bebenlebricolo/LabBenchPowerSupply/Simulations/MosfetDriverAntiLatchup.asc

C1: cap; 10µ
Q1: npn; 2N2222
Q2: pnp; 2N2907
Q3: npn; 2N2222
Q4: pnp; 2N2907
R1: res; 1k
R2: res; 56k
R3: res; 1k
R4: res; 56k
R5: res; 56k
R6: res; 1k
R7: res; 56k
R8: res; 1k
R9: res; 200
V1: voltage; 5
V2: voltage; 10
V3: signal; PULSE(0 5 0 1n 1n 10m 20m 250)
Named nets: 0, 5V, 10V
.tran 0 100m 1m 100u
