bebenlebricolo/LabBenchPowerSupply/Simulations/MosfetDriverAntiLatchup_P.asc

C1: cap; 470µ
D1: schottky; MBR745
L1: ind; 110µ
M1: pmos; FDC5614P
Q1: npn; 2N2222
Q2: pnp; 2N2907
Q3: npn; 2N2222
Q4: npn; 2N2222
R1: res; 1k
R2: res; 56k
R3: res; 1k
R4: res; 56k
R5: res; 56k
R6: res; 1k
R7: res; 10
R8: res; 1k
R9: res; 56k
V1: voltage; 5
V2: voltage; 30
V3: signal; PULSE(0 5 0 1n 1n 10m 20m 250)
V4: signal; PULSE(0 5 11m 1n 1n 8m 20m 250)
Named nets: 0, 5V, DriverSupply, high_side, low_side, MosfetGate
.tran 0 100m 1m 100u
