bebenlebricolo/LabBenchPowerSupply/Simulations/BuckConverter.asc

C1: cap; 470µ
C2: cap; 1µ
D1: schottky; MBR0530L
L1: ind; 110µ; Ipk=7
M1: nmos; AP9465GEM
R1: res; 1
R2: res; 0.1
U2: AD8032
V1: voltage; 12
V2: signal; PULSE(0 12 0 1n 1n 30u 50u 5K)
Named nets: 0, Mosfet_control, Out, Vshunt, Vcc, FilteredVshunt
.tran 0 20m 1n 1m startup
