bebenlebricolo/LabBenchPowerSupply/Firmware/Drivers/Adc/inc/adc.h

/*

------------------
@<FreeMyCode>
FreeMyCode version : 1.0 RC alpha
    Author : bebenlebricolo
    License : 
        name : GPLv3
        url : https://www.gnu.org/licenses/quick-guide-gplv3.html
    Date : 12/02/2021
    Project : LabBenchPowerSupply
    Description : The Lab Bench Power Supply provides a simple design based around an Arduino Nano board to convert AC main voltage into
 smaller ones, ranging from 0V to 16V, with voltage and current regulations
<FreeMyCode>@
------------------

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
You should have received a copy of the GNU General Public License
along with this program.  If not, see <https://www.gnu.org/licenses/>.
*/

/**
 * @brief ADC custom driver
*/
#ifndef ADC_HEADER
#define ADC_HEADER

/* Expose this API to C++ code without name mangling */
#ifdef __cplusplus
extern "C"
{
#endif /* __cplusplus */

/* Generic includes */
#include <stdint.h>
#include <stddef.h>
#include <stdbool.h>

/* Application drivers */
#include "adc_reg.h"

/* ############################################################################################
   ################################## Data types declaration ##################################
   ############################################################################################ */

typedef uint16_t adc_result_t;
typedef uint16_t adc_millivolts_t;


/**
 * @brief generic structure which holds timer error types
*/
typedef enum
{
    ADC_ERROR_OK,               /**< Everything went well so far                                  */
    ADC_ERROR_CONFIG,           /**< Given configuration is not well-formed                       */
    ADC_ERROR_CHANNEL_NOT_FOUND,/**< Given configuration is not well-formed                       */
    ADC_ERROR_NULL_POINTER,     /**< One or more parameters were set to NULL                      */
    ADC_ERROR_NULL_HANDLE,      /**< Timer handle still points to NULL                            */
    ADC_ERROR_UNKNOWN_TIMER,    /**< Given timer id exceeds the range of registered timers        */
    ADC_ERROR_NOT_INITIALISED,  /**< Given configuration is not well-formed                       */
} adc_error_t;

/**
 * @brief basic adc peripheral state
*/
typedef enum
{
    ADC_STATE_READY,              /**< Adc is initialised and is ready                */
    ADC_STATE_BUSY,               /**< A conversion is ongoing, peripheral is busy    */
    ADC_STATE_NOT_INITIALISED,    /**< Driver is not initialised                      */
} adc_state_t;

/**
 * @brief gives running modes of ADC driver
*/
typedef enum
{
    ADC_RUNNING_MODE_SINGLE_SHOT,   /**< If set, adc will require start() to be called repeateadly between each calls       */
    ADC_RUNNING_MODE_AUTOTRIGGERED  /**< ADC is controlled by a trigger event, which my be set to free-running (software)
                                         in this particular case, ADC will be continuously triggered when a conversion ends  */
}adc_running_mode_t;

/**
 * @brief this structure mimics ADC peripheral registers. It is passed when configuring ADC peripheral.
 */
typedef struct {
    volatile uint8_t  *  mux_reg;    /**< Refers to adc multiplexing register (ADCMUX)   */
    volatile uint8_t  *  adcsra_reg; /**< Refers to ADC Control and Status Register A    */
    volatile uint8_t  *  adcsrb_reg; /**< Refers to ADC Control and Status Register B    */

    /* Packs result registers in one */
    struct {
        volatile uint8_t *  adclow_reg;  /**< Refers to the low value register of ADC peripheral  (first 8 bits)*/
        volatile uint8_t *  adchigh_reg; /**< Refers to the high value register of ADC peripheral (last 2 bits) */
    } readings;
} adc_handle_t;

/* Configuration structure of ADC module */
typedef struct {
    uint16_t                    supply_voltage_mv;  /**< MCU supply voltage in millivolts                       */
    adc_prescaler_t             prescaler;          /**< ADC internal prescaler                                 */
    adc_voltage_ref_t           ref;                /**< ADC reference voltage                                  */
    adc_result_align_t          alignment;          /**< ADC data alignment                                     */
    adc_running_mode_t          running_mode;       /**< Select the mode between continous or single shot       */
    adc_autotrigger_sources_t   trigger_sources;    /**< ADC trigger mode                                       */
    adc_handle_t                handle;             /**< Packs pointers to base ADC registers. Particularly
                                                         useful when performing Dependency Injection & testing  */
    bool using_interrupt;                           /**< uses interrupts for data fetch process or not          */
} adc_config_hal_t;


/* ############################################################################################
   #################################### Types manipulators ####################################
   ############################################################################################ */

/**
 * @brief copies a configuration from a source pointer to a destination pointer
 * @param[in]   src     : pointer to source object
 * @param[out]  dest    : pointer to destination object
 * @return
 *      PERIPHERAL_ERROR_OK             : operation succeeded
 *      PERIPHERAL_ERROR_NULL_POINTER   : null pointer guarded
*/
adc_error_t adc_config_hal_copy(adc_config_hal_t * dest, adc_config_hal_t * const src);

/**
 * @brief resets config to default
 * @param[in]   config : pointer to configuration object
 * @return
 *      PERIPHERAL_ERROR_OK             : operation succeeded
 *      PERIPHERAL_ERROR_NULL_POINTER   : null pointer guarded
*/
adc_error_t adc_config_hal_reset(adc_config_hal_t * config);

/**
 * @brief returns a default configuration for the ADC driver
 * @param[out]  config : pointer to configuration object
 * @return
 *      PERIPHERAL_ERROR_OK             : operation succeeded
 *      PERIPHERAL_ERROR_NULL_POINTER   : null pointer guarded
*/
adc_error_t adc_config_hal_get_default(adc_config_hal_t * config);

/**
 * @brief copies handle data from a source object to destination object
 * @param[in]   src     : pointer to source object
 * @param[out]  dest    : pointer to destination object
 * @return
 *      PERIPHERAL_ERROR_OK             : operation succeeded
 *      PERIPHERAL_ERROR_NULL_POINTER   : null pointer guarded
*/
adc_error_t adc_handle_copy(adc_handle_t * const dest, const adc_handle_t * const src);

/**
 * @brief resets handle to default
 * @param[in]   handle : pointer to handle object
 * @return
 *      PERIPHERAL_ERROR_OK             : operation succeeded
 *      PERIPHERAL_ERROR_NULL_POINTER   : null pointer guarded
*/
adc_error_t adc_handle_reset(adc_handle_t * const handle);

/* ############################################################################################
   ################################## Function declarations ###################################
   ############################################################################################ */

/**
 * @brief adc module initialisation function
*/
adc_error_t adc_base_init(adc_config_hal_t * const config);

/**
 * @brief module deinitialisation
*/
void adc_base_deinit(void);

/**
 * @brief starts the adc in normal mode, no interrupt set
 * @see adc_state_t adc_process() to be able to fetch results from adc registers and post result to internal buffer
 * Note: one must use functions in this order :
 *    - adc_base_init() // done once
 *    - adc_start()     // starts peripheral
 *    - repeat :
 *       - if interrupt mode is not set : adc_process()   // fetches result from adc peripheral
 *       - adc_read_raw()       // return results to application
 *    OR - adc_read_millivolt() // instead to retrieve actual voltage instead of raw value
 *    - adc_stop()      // stops the adc
 * @return
 *      PERIPHERAL_ERROR_OK      : operation was successful
 *      ADC_ERROR_CONFIG  : adc peripheral is not enabled (not initialised ?)
*/
adc_state_t adc_start(void);

/**
 * @brief stops the adc in normal mode, no interrupt
 * @return
 *      PERIPHERAL_ERROR_OK      : operation was successful
 *      ADC_ERROR_CONFIG  : adc peripheral is not enabled (not initialised ?)
*/
adc_state_t adc_stop(void);

/**
 * @brief starts conversions and retrieves results (using asynchronous, non interrupting mode)
 * @return
 *      PERIPHERAL_ERROR_OK      : operation was successful
 *      ADC_ERROR_CONFIG  : adc peripheral is not enabled (not initialised ?)
*/
adc_state_t adc_process(void);

/**
 * @brief isr handler that might be called from within an ISR function
*/
void adc_isr_handler(void);

/**
 * @brief explicitely adds a channel to scanned channels configuration
 * @param[in]   channel : channel to be configured and scanned */
adc_error_t adc_register_channel(const adc_mux_t channel);

/**
 * @brief explicitely removes channel from scanned channels configuration
 * @param[in]   channel : channel to be removed */
adc_error_t adc_unregister_channel(const adc_mux_t channel);

/**
 * @brief adc result getter function
 * @param[in]   channel  : targeted device index
 * @param[out]  result   : last fetched result from this device
 * @return
 *      PERIPHERAL_ERROR_OK             : everything's fine
 *      PERIPHERAL_ERROR_NULL_POINTER   : wrong pointer or out of bounds index
*/
adc_error_t adc_read_raw(const adc_mux_t channel, adc_result_t * const result);

/**
 * @brief adc raw reading getter
 * @param[in]   channel   : targeted device index
 * @param[out]  reading : last fetched result from this device
 * @return
 *      PERIPHERAL_ERROR_OK      : everything's fine
 *      PERIPHERAL_ERROR_NULL_POINTER  : wrong pointer or out of bounds index
*/
adc_error_t adc_read_millivolt(const adc_mux_t channel, adc_millivolts_t * const reading);


#ifdef __cplusplus
}
#endif

#endif /* ADC_HEADER */
