bebenlebricolo/LabBenchPowerSupply/Firmware/Sensors/Thermistor/Tests/thermistor_driver_tests.cpp

/*

------------------
@<FreeMyCode>
FreeMyCode version : 1.0 RC alpha
    Author : bebenlebricolo
    License :
        name : GPLv3
        url : https://www.gnu.org/licenses/quick-guide-gplv3.html
    Date : 12/02/2021
    Project : LabBenchPowerSupply
    Description : The Lab Bench Power Supply provides a simple design based around an Arduino Nano board to convert AC main voltage into
 smaller ones, ranging from 0V to 16V, with voltage and current regulations
<FreeMyCode>@
------------------

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
You should have received a copy of the GNU General Public License
along with this program.  If not, see <https://www.gnu.org/licenses/>.
*/

#include "gtest/gtest.h"

#include "config.h"
#include "adc_stub.h"
#include "thermistor.h"
#include "thermistor_private.h"

TEST(thermistor_tests, test_find_segment)
{
    uint8_t target_ratio = 11;
    thermistor_curve_discrete_pair_t const * lower_bound = NULL;
    thermistor_curve_discrete_pair_t const * upper_bound = NULL;
    bool ret = find_segment(thermistor_driver_config[0].model.curve.data.discrete.cold_side, target_ratio, RATIO_COEF_1, &lower_bound, &upper_bound );
    ASSERT_TRUE(ret);
    ASSERT_EQ(lower_bound->ratio, 12U);
    ASSERT_EQ(upper_bound->ratio, 8U);

    // Using the x10 representation, actual ratio is 8
    target_ratio = 80U;
    ret = find_segment(thermistor_driver_config[0].model.curve.data.discrete.cold_side, target_ratio,  RATIO_COEF_10, &lower_bound, &upper_bound );
    ASSERT_TRUE(ret);
    ASSERT_EQ(lower_bound->ratio, 8U);
    ASSERT_EQ(upper_bound->ratio, 8U);
    ASSERT_EQ(lower_bound, upper_bound);

    // Using the x10 representation, actual ratio is 8
    target_ratio = 63U;
    ret = find_segment(thermistor_driver_config[0].model.curve.data.discrete.cold_side, target_ratio,  RATIO_COEF_10, &lower_bound, &upper_bound );
    ASSERT_TRUE(ret);
    ASSERT_EQ(lower_bound->ratio, 8U);
    ASSERT_EQ(upper_bound->ratio, 4U);

    // Using the x100 representation, actual ratio is 0.53 (53%)
    target_ratio = 53U;
    ret = find_segment(thermistor_driver_config[0].model.curve.data.discrete.hot_side, target_ratio,  RATIO_COEF_100, &lower_bound, &upper_bound );
    ASSERT_TRUE(ret);
    ASSERT_EQ(lower_bound->ratio, 100U);
    ASSERT_EQ(upper_bound->ratio, 25U);

    // Using the x100 representation, actual ratio is 0.53 (53%)
    target_ratio = 0U;
    ret = find_segment(thermistor_driver_config[0].model.curve.data.discrete.hot_side, target_ratio,  RATIO_COEF_100, &lower_bound, &upper_bound );
    ASSERT_FALSE(ret);
    ASSERT_EQ(lower_bound->ratio, 1U);
    ASSERT_EQ(upper_bound->ratio, 1U);
}

TEST(thermistor_tests, test_compute_ratios)
{
    // Cold side first
    adc_millivolts_t reading = 2125U;
    uint8_t ratio = 0;
    ratio_coefficients_t coef = compute_ratio(&thermistor_driver_config[0].model, &reading, &ratio);
    ASSERT_EQ(coef, RATIO_COEF_10);
    ASSERT_EQ(ratio, 13U);

    reading = 1200U;
    coef = compute_ratio(&thermistor_driver_config[0].model, &reading, &ratio);
    ASSERT_EQ(coef, RATIO_COEF_10);
    ASSERT_EQ(ratio, 31U);

    reading = 250U;
    coef = compute_ratio(&thermistor_driver_config[0].model, &reading, &ratio);
    ASSERT_EQ(coef, RATIO_COEF_1);
    ASSERT_EQ(ratio, 19);

    reading = 120U;
    coef = compute_ratio(&thermistor_driver_config[0].model, &reading, &ratio);
    ASSERT_EQ(coef, RATIO_COEF_1);
    ASSERT_EQ(ratio, 40);

    // Hot side
    reading = 3000U;
    coef = compute_ratio(&thermistor_driver_config[0].model, &reading, &ratio);
    ASSERT_EQ(coef, RATIO_COEF_100);
    ASSERT_EQ(ratio, 65);

    reading = 4500U;
    coef = compute_ratio(&thermistor_driver_config[0].model, &reading, &ratio);
    ASSERT_EQ(coef, RATIO_COEF_100);
    ASSERT_EQ(ratio, 10U);
}

TEST(thermistor_tests, test_compute_temperature)
{
    adc_millivolts_t reading = 2125U;
    int8_t temp = compute_temperature(0, &reading);
    ASSERT_EQ(temp, 23U);

    reading = 2500U;
    temp = compute_temperature(0, &reading);
    ASSERT_EQ(temp, 25U);

    reading = 2700U;
    temp = compute_temperature(0, &reading);
    ASSERT_EQ(temp, 27U);

    reading = 3200U;
    temp = compute_temperature(0, &reading);
    ASSERT_EQ(temp, 33U);

    reading = 4123U;
    temp = compute_temperature(0, &reading);
    ASSERT_EQ(temp, 42U);

    reading = 4980U;
    temp = compute_temperature(0, &reading);
    ASSERT_EQ(temp, 77);
}


TEST(thermistor_tests, test_process_sensors)
{
    adc_millivolts_t reading = 2125U;
    thermistor_error_t error = THERMISTOR_ERR_OK;
    int8_t temperature = 0;
    stub_adc_set_readings(THERMISTOR_CONFIG_ADC_INDEX, reading);

    stub_adc_set_error(ADC_ERROR_CONFIG);
    error = thermistor_process();
    ASSERT_EQ(error, THERMISTOR_ERR_WRONG_CONFIG);

    stub_adc_register_channel(ADC_MUX_ADC1);

    stub_adc_set_error(ADC_ERROR_OK);
    error = thermistor_process();
    ASSERT_EQ(error, THERMISTOR_ERR_OK);
    error = thermistor_read(0U, &temperature);
    EXPECT_EQ(temperature, 23U);

    reading = 2000;
    stub_adc_set_readings(THERMISTOR_CONFIG_ADC_INDEX, reading);
    error = thermistor_process();
    ASSERT_EQ(error, THERMISTOR_ERR_OK);
    error = thermistor_read(0U, &temperature);
    ASSERT_EQ(error, THERMISTOR_ERR_OK);
    EXPECT_EQ(temperature, 22);

    reading = 3200U;
    stub_adc_set_readings(THERMISTOR_CONFIG_ADC_INDEX, reading);
    error = thermistor_process();
    ASSERT_EQ(error, THERMISTOR_ERR_OK);
    error = thermistor_read(0U, &temperature);
    ASSERT_EQ(error, THERMISTOR_ERR_OK);
    EXPECT_EQ(temperature, 33);

    reading = 4980U;
    stub_adc_set_readings(THERMISTOR_CONFIG_ADC_INDEX, reading);
    error = thermistor_process();
    ASSERT_EQ(error, THERMISTOR_ERR_OK);
    error = thermistor_read(0U, &temperature);
    ASSERT_EQ(error, THERMISTOR_ERR_OK);
    EXPECT_EQ(temperature, 77);

}

int main(int argc, char **argv)
{
    ::testing::InitGoogleTest(&argc, argv);
    return RUN_ALL_TESTS();
}
