bebenlebricolo/LabBenchPowerSupply/Firmware/Drivers/Lcd_screen/Examples/App/inc/config.h

#ifndef CONFIG_HEADER
#define CONFIG_HEADER

/* Defines how many instances of timer/counters will be created */
#define TIMER_8_BIT_COUNT       1
#define TIMER_8_BIT_ASYNC_COUNT 1
#define TIMER_16_BIT_COUNT      1

#define TIMEBASE_MAX_MODULES 3U
#define I2C_DEVICES_COUNT 1U

#endif /* CONFIG_HEADER */
