bebenlebricolo/LabBenchPowerSupply/Firmware/Drivers/I2c/Tests/Stub/i2c_fake_slave_application_data.h

/*

------------------
@<FreeMyCode>
FreeMyCode version : 1.0 RC alpha
    Author : bebenlebricolo
    License : 
        name : GPLv3
        url : https://www.gnu.org/licenses/quick-guide-gplv3.html
    Date : 12/02/2021
    Project : LabBenchPowerSupply
    Description : The Lab Bench Power Supply provides a simple design based around an Arduino Nano board to convert AC main voltage into
 smaller ones, ranging from 0V to 16V, with voltage and current regulations
<FreeMyCode>@
------------------

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
You should have received a copy of the GNU General Public License
along with this program.  If not, see <https://www.gnu.org/licenses/>.
*/

#ifndef I2C_FAKE_SLAVE_APPLICATION_DATA
#define I2C_FAKE_SLAVE_APPLICATION_DATA

#ifdef __cplusplus
extern "C"
{
#endif

#include "i2c.h"
#define I2C_FAKE_SLAVE_APPLICATION_DATA_MAX_BYTE_ARRAY_LENGTH (30U)

/**
 * @brief Fake commands that could be used to simulate an application firmware code
*/
typedef enum
{
    I2C_FAKE_SLAVE_APPLICATION_DATA_CMD_UNDEFINED,      /**< Default command code, this result in an invalid request (NACK might be returned when device is processed)  */
    I2C_FAKE_SLAVE_APPLICATION_DATA_CMD_FAN_SPEED,      /**< Sets the internal buffer to a FAN_SPEED register                                                           */
    I2C_FAKE_SLAVE_APPLICATION_DATA_CMD_BYTE_ARRAY,     /**< Exposes a multi-bytes register to I2C device (could be anything, e.g. error message, pointsets, etc.)      */
    I2C_FAKE_SLAVE_APPLICATION_DATA_CMD_MAX_CURRENT,    /**< Register controlling maximum current                                                                       */
    I2C_FAKE_SLAVE_APPLICATION_DATA_CMD_MAX_VOLTAGE,    /**< Register controlling maximum voltage                                                                       */
    I2C_FAKE_SLAVE_APPLICATION_DATA_CMD_ENABLED,        /**< Register controlling the behavior of slave device (enabled/disabled)                                       */
} i2c_fake_slave_application_data_available_commands_t;

typedef enum
{
    I2C_FAKE_SLAVE_APPLICATION_DATA_FAN_SPEED_0,
    I2C_FAKE_SLAVE_APPLICATION_DATA_FAN_SPEED_25,
    I2C_FAKE_SLAVE_APPLICATION_DATA_FAN_SPEED_50,
    I2C_FAKE_SLAVE_APPLICATION_DATA_FAN_SPEED_75,
    I2C_FAKE_SLAVE_APPLICATION_DATA_FAN_SPEED_100,
} i2c_fake_slave_application_data_fan_speed_t;
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
